mekhaelt/Aim-Assist/hardware/solidworks_design_files/gear_small.SLDPRT

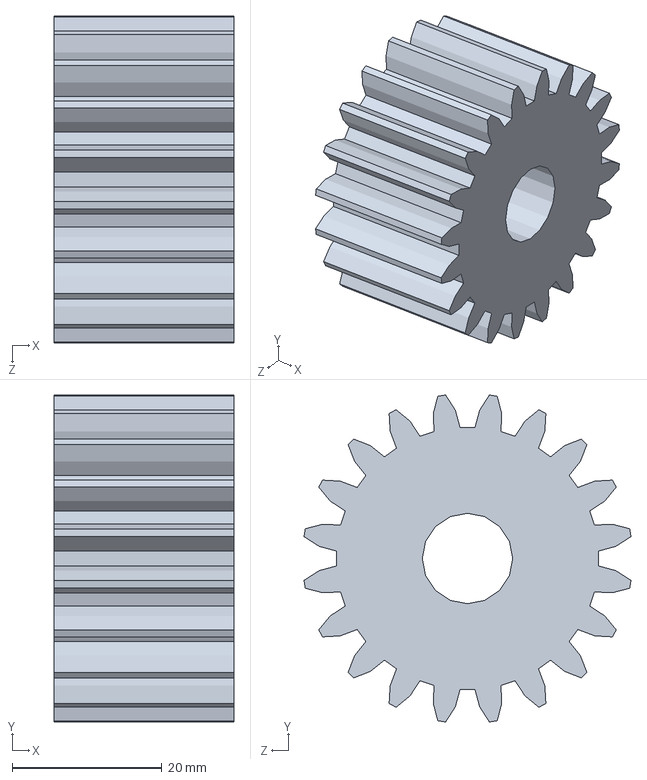
[picture p39: CAD file, 2024-08-16]
hardware/solidworks_design_files/gear_small.SLDPRT
24.0 x 43.6 x 43.6 mm
