mekhaelt/Aim-Assist/hardware/solidworks_design_files/arduino_uno_template.SLDPRT

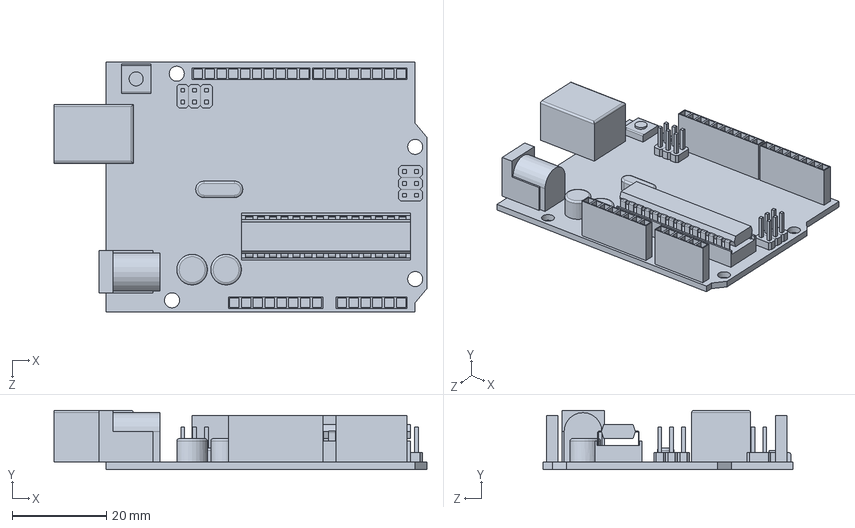
[picture p40: CAD file, 2024-08-16]
hardware/solidworks_design_files/arduino_uno_template.SLDPRT
79.0 x 12.6 x 53.0 mm
