mekhaelt/Aim-Assist/gallery/Schematic-AimAssist.asc

AI: AD623
C1: cap; 0.1µ
C2: cap; 1µ
C3: cap; 0.1µ
C4: cap; 3.3n
C5: cap; 33n
C6: cap; 1µ
D1: diode; 1N4148
D2: diode; 1N4148
D3: diode; 1N4148
HP-LM741: UniversalOpAmp2; Avol=0.14Meg GBW=1.2Meg Slew=0.5Meg; Ilimit=25m Rail=0 Vos=0.2e-3
HWR-LM741: UniversalOpAmp2; Avol=0.14Meg GBW=1.2Meg Slew=0.5Meg; Ilimit=25m Rail=0 Vos=0.2e-3
IA-LM741: UniversalOpAmp2; Avol=0.14Meg GBW=1.2Meg Slew=0.5Meg; Ilimit=25m Rail=0 Vos=0.2e-3
LP-LM741: UniversalOpAmp2; Avol=0.14Meg GBW=1.2Meg Slew=0.5Meg; Ilimit=25m Rail=0 Vos=0.2e-3
PD-LM741: UniversalOpAmp2; Avol=0.14Meg GBW=1.2Meg Slew=0.5Meg; Ilimit=25m Rail=0 Vos=0.2e-3
R1: res; 100
R2: res; 1k
R3: res; 1k
R4: res; 500k
R5: res; 50k
R6: res; 27k
R7: res; 27k
R8: res; 10k
R9: res; 20k
R10: res; 10k
R11: res; 10k
R12: res; 20k
R13: res; 10k
R14: res; 20k
R15: res; 300k
SA-LM741: UniversalOpAmp2; Avol=0.14Meg GBW=1.2Meg Slew=0.5Meg; Ilimit=25m Rail=0 Vos=0.2e-3
V1: voltage; 0
V2: voltage; SINE(0 1mV 200)
V+: voltage; 5
VB-LM741: UniversalOpAmp2; Avol=0.14Meg GBW=1.2Meg Slew=0.5Meg; Ilimit=25m Rail=0 Vos=0.2e-3
Vref: voltage
Named nets: 0, V+, Vref, +V, Vout
